Lululululululululululul/Projet-Synthe/hardware / Monostation.kicad_sch

## KiCad design hardware / Monostation.kicad_sch (2026-06-28)

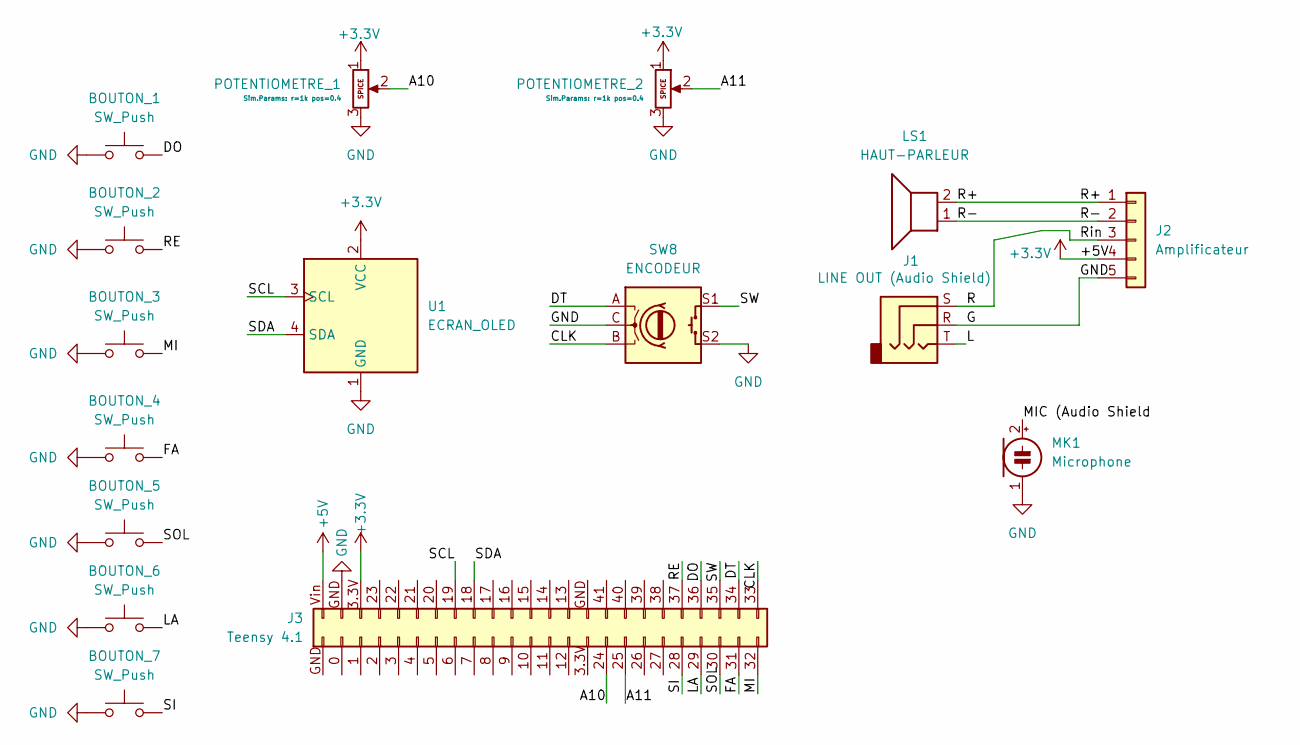
[picture p2: schematic Monostation.kicad_sch]

Parts:
BOUTON_1, BOUTON_2, BOUTON_3, BOUTON_4, BOUTON_5, BOUTON_6, BOUTON_7: SW_Push
J1: LINE OUT (Audio Shield)
J2: Amplificateur
J3: Teensy 4.1
LS1: HAUT-PARLEUR
MK1: Microphone
POTENTIOMETRE_1, POTENTIOMETRE_2: Potentiometer
SW8: ENCODEUR
U1: ECRAN_OLED; ER_OLEDM0.91_1x-I2C

Connections:
+3.3V: J2.4, J3.3.3V (Pin_15), POTENTIOMETRE_1.1, POTENTIOMETRE_2.1, U1.2 (VCC)
+5V: J3.Vin (Pin_48)
A10: J3.24 (Pin_16), POTENTIOMETRE_1.2
A11: J3.25 (Pin_17), POTENTIOMETRE_2.2
CLK: J3.33 (Pin_25), SW8.B
DO: BOUTON_1.2, J3.36 (Pin_28)
DT: J3.34 (Pin_26), SW8.A
FA: BOUTON_4.2, J3.31 (Pin_23)
G: J1.R, J2.5, SW8.C
GND: BOUTON_1.1, BOUTON_2.1, BOUTON_3.1, BOUTON_4.1, BOUTON_5.1, BOUTON_6.1, BOUTON_7.1, J3.GND (Pin_1), MK1.1 (-), POTENTIOMETRE_1.3, POTENTIOMETRE_2.3, SW8.S2, U1.1 (GND)
L: J1.T
LA: BOUTON_6.2, J3.29 (Pin_21)
MI: BOUTON_3.2, J3.32 (Pin_24)
MIC (Audio Shield: MK1.2 (+)
R: J1.S, J2.3
R+: J2.1, LS1.2
R-: J2.2, LS1.1
RE: BOUTON_2.2, J3.37 (Pin_29)
SCL: J3.19 (Pin_41), U1.3 (SCL)
SDA: J3.18 (Pin_40), U1.4 (SDA)
SI: BOUTON_7.2, J3.28 (Pin_20)
SOL: BOUTON_5.2, J3.30 (Pin_22)
SW: J3.35 (Pin_27), SW8.S1
